Emeryth/Ergo72/ErgoDOX.sch

## KiCad design ErgoDOX.sch (2020-08-02, an earlier design)

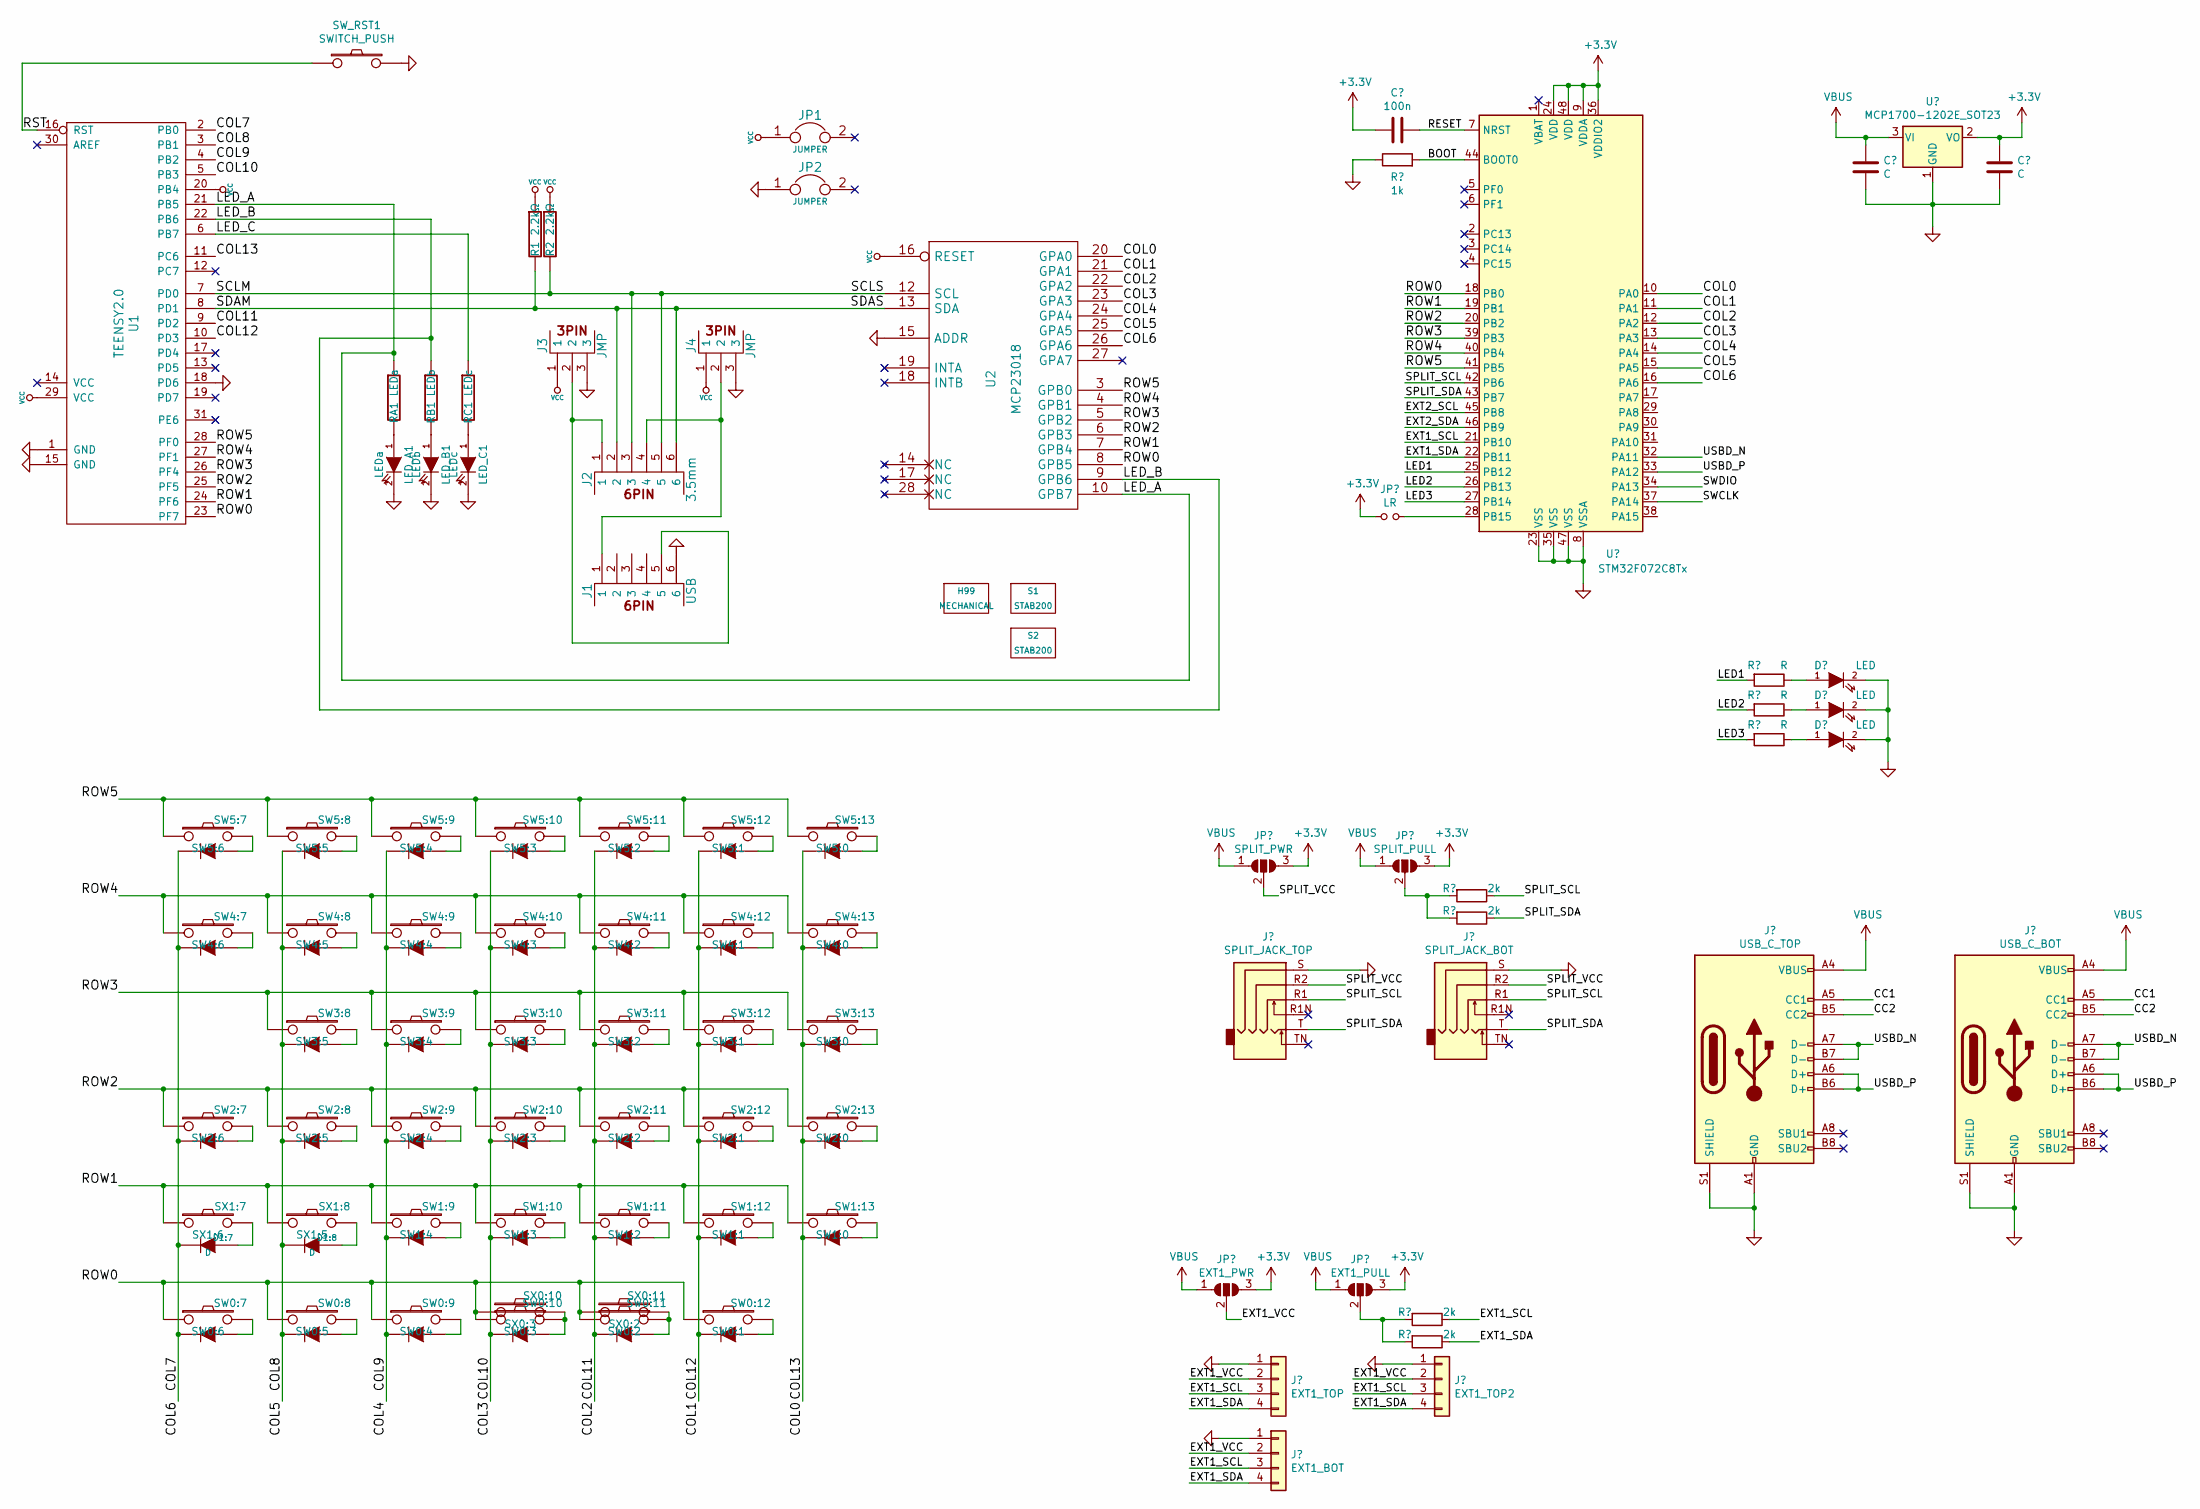
[picture p8: schematic ErgoDOX.sch]

Parts:
D1:7, D1:8: D
H99: MECHANICAL
J1: USB
J2: 3.5mm
J3, J4: JMP
JP1, JP2: JUMPER
LED_A1: LEDa
LED_B1: LEDb
LED_C1: LEDc
R1, R2: 2.2kΩ
RA1: LEDa
RB1: LEDb
RC1: LEDc
S1, S2: STAB200
SW0:7: SW0:6
SW0:8: SW0:5
SW0:9: SW0:4
SW0:10: SW0:3
SW0:11: SW0:2
SW0:12: SW0:1
SW1:9: SW1:4
SW1:10: SW1:3
SW1:11: SW1:2
SW1:12: SW1:1
SW1:13: SW1:0
SW2:7: SW2:6
SW2:8: SW2:5
SW2:9: SW2:4
SW2:10: SW2:3
SW2:11: SW2:2
SW2:12: SW2:1
SW2:13: SW2:0
SW3:8: SW3:5
SW3:9: SW3:4
SW3:10: SW3:3
SW3:11: SW3:2
SW3:12: SW3:1
SW3:13: SW3:0
SW4:7: SW4:6
SW4:8: SW4:5
SW4:9: SW4:4
SW4:10: SW4:3
SW4:11: SW4:2
SW4:12: SW4:1
SW4:13: SW4:0
SW5:7: SW5:6
SW5:8: SW5:5
SW5:9: SW5:4
SW5:10: SW5:3
SW5:11: SW5:2
SW5:12: SW5:1
SW5:13: SW5:0
SW_RST1: SWITCH_PUSH; SW_SPST_B3U-1000P
SX0:10: SX0:3
SX0:11: SX0:2
SX1:7: SX1:6
SX1:8: SX1:5
U1: TEENSY2.0
U2: MCP23018

Connections:
COL0: SW1:13.4 (K), SW2:13.4 (K), SW3:13.4 (K), SW4:13.4 (K), SW5:13.4 (K), U1.11 (PC6), U2.20 (GPA0)
COL1: SW0:12.4 (K), SW1:12.4 (K), SW2:12.4 (K), SW3:12.4 (K), SW4:12.4 (K), SW5:12.4 (K), U1.10 (PD3), U2.21 (GPA1)
COL4: SW0:9.4 (K), SW1:9.4 (K), SW2:9.4 (K), SW3:9.4 (K), SW4:9.4 (K), SW5:9.4 (K), U1.4 (PB2), U2.24 (GPA4)
COL5: D1:8.2 (K), SW0:8.4 (K), SW2:8.4 (K), SW3:8.4 (K), SW4:8.4 (K), SW5:8.4 (K), U1.3 (PB1), U2.25 (GPA5)
COL6: D1:7.2 (K), SW0:7.4 (K), SW2:7.4 (K), SW4:7.4 (K), SW5:7.4 (K), U1.2 (PB0), U2.26 (GPA6)
COL10: SW0:10.4 (K), SW1:10.4 (K), SW2:10.4 (K), SW3:10.4 (K), SW4:10.4 (K), SW5:10.4 (K), U1.5 (PB3), U2.23 (GPA3)
COL11: SW0:11.4 (K), SW1:11.4 (K), SW2:11.4 (K), SW3:11.4 (K), SW4:11.4 (K), SW5:11.4 (K), U1.9 (PD2), U2.22 (GPA2)
GND: J1.6, J3.3, J4.3, JP2.1, LED_A1.2 (K), LED_B1.2 (K), LED_C1.2 (K), SW_RST1.2, U1.1 (GND), U1.15 (GND), U1.18 (PD6), U2.15 (ADDR)
LED_A: RA1.1, U1.21 (PB5), U2.10 (GPB7)
LED_B: RB1.1, U1.22 (PB6), U2.9 (GPB6)
LED_C: RC1.1, U1.6 (PB7)
unnamed: D1:7.1 (A), SX1:7.2
unnamed: D1:8.1 (A), SX1:8.2
unnamed: J1.1, J2.4, J4.2
unnamed: J1.5, J2.1, J3.2
unnamed: LED_A1.1 (A), RA1.2
unnamed: LED_B1.1 (A), RB1.2
unnamed: LED_C1.1 (A), RC1.2
unnamed: SW0:7.2, SW0:7.3 (A)
unnamed: SW0:8.2, SW0:8.3 (A)
unnamed: SW0:9.2, SW0:9.3 (A)
unnamed: SW0:10.2, SW0:10.3 (A), SX0:10.2
unnamed: SW0:11.2, SW0:11.3 (A), SX0:11.2
unnamed: SW0:12.2, SW0:12.3 (A)
unnamed: SW1:9.2, SW1:9.3 (A)
unnamed: SW1:10.2, SW1:10.3 (A)
unnamed: SW1:11.2, SW1:11.3 (A)
unnamed: SW1:12.2, SW1:12.3 (A)
unnamed: SW1:13.2, SW1:13.3 (A)
unnamed: SW2:7.2, SW2:7.3 (A)
unnamed: SW2:8.2, SW2:8.3 (A)
unnamed: SW2:9.2, SW2:9.3 (A)
unnamed: SW2:10.2, SW2:10.3 (A)
unnamed: SW2:11.2, SW2:11.3 (A)
unnamed: SW2:12.2, SW2:12.3 (A)
unnamed: SW2:13.2, SW2:13.3 (A)
unnamed: SW3:8.2, SW3:8.3 (A)
unnamed: SW3:9.2, SW3:9.3 (A)
unnamed: SW3:10.2, SW3:10.3 (A)
unnamed: SW3:11.2, SW3:11.3 (A)
unnamed: SW3:12.2, SW3:12.3 (A)
unnamed: SW3:13.2, SW3:13.3 (A)
unnamed: SW4:7.2, SW4:7.3 (A)
unnamed: SW4:8.2, SW4:8.3 (A)
unnamed: SW4:9.2, SW4:9.3 (A)
unnamed: SW4:10.2, SW4:10.3 (A)
unnamed: SW4:11.2, SW4:11.3 (A)
unnamed: SW4:12.2, SW4:12.3 (A)
unnamed: SW4:13.2, SW4:13.3 (A)
unnamed: SW5:7.2, SW5:7.3 (A)
unnamed: SW5:8.2, SW5:8.3 (A)
unnamed: SW5:9.2, SW5:9.3 (A)
unnamed: SW5:10.2, SW5:10.3 (A)
unnamed: SW5:11.2, SW5:11.3 (A)
unnamed: SW5:12.2, SW5:12.3 (A)
unnamed: SW5:13.2, SW5:13.3 (A)
ROW0: SW0:7.1, SW0:8.1, SW0:9.1, SW0:10.1, SW0:11.1, SW0:12.1, SX0:10.1, SX0:11.1, U1.23 (PF7), U2.8 (GPB5)
ROW1: SW1:9.1, SW1:10.1, SW1:11.1, SW1:12.1, SW1:13.1, SX1:7.1, SX1:8.1, U1.24 (PF6), U2.7 (GPB4)
ROW2: SW2:7.1, SW2:8.1, SW2:9.1, SW2:10.1, SW2:11.1, SW2:12.1, SW2:13.1, U1.25 (PF5), U2.6 (GPB3)
ROW3: SW3:8.1, SW3:9.1, SW3:10.1, SW3:11.1, SW3:12.1, SW3:13.1, U1.26 (PF4), U2.5 (GPB2)
ROW4: SW4:7.1, SW4:8.1, SW4:9.1, SW4:10.1, SW4:11.1, SW4:12.1, SW4:13.1, U1.27 (PF1), U2.4 (GPB1)
ROW5: SW5:7.1, SW5:8.1, SW5:9.1, SW5:10.1, SW5:11.1, SW5:12.1, SW5:13.1, U1.28 (PF0), U2.3 (GPB0)
RST: SW_RST1.1, U1.16 (RST)
SCLM: J2.3, J2.5, R2.2, U1.7 (PD0), U2.12 (SCL)
SDAM: J2.2, J2.6, R1.2, U1.8 (PD1), U2.13 (SDA)
VCC: J3.1, J4.1, JP1.1, R1.1, R2.1, U1.20 (PB4), U1.29 (VCC), U2.16 (RESET)
